plyalex/OpenFence/hardware/pcbs/MainCollar/MainCollarRender.jpg

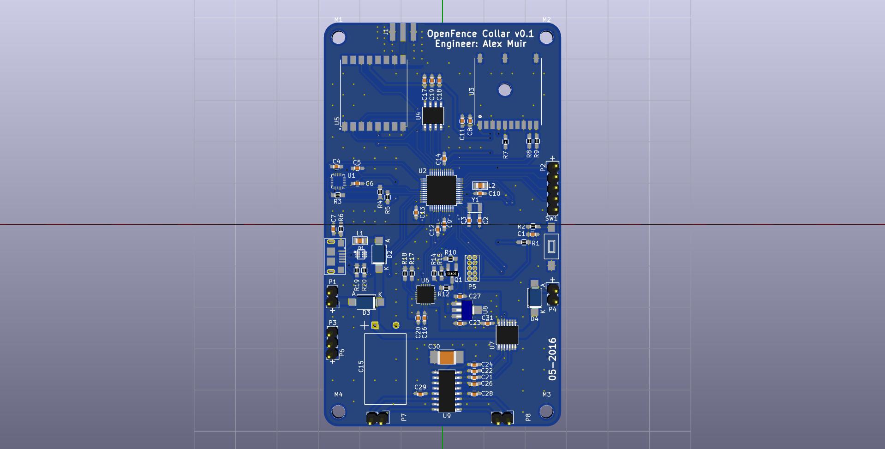
hardware/pcbs/MainCollar/MainCollarRender.jpg
