plyalex/OpenFence/hardware/solidworks/basestation/toplink.SLDPRT

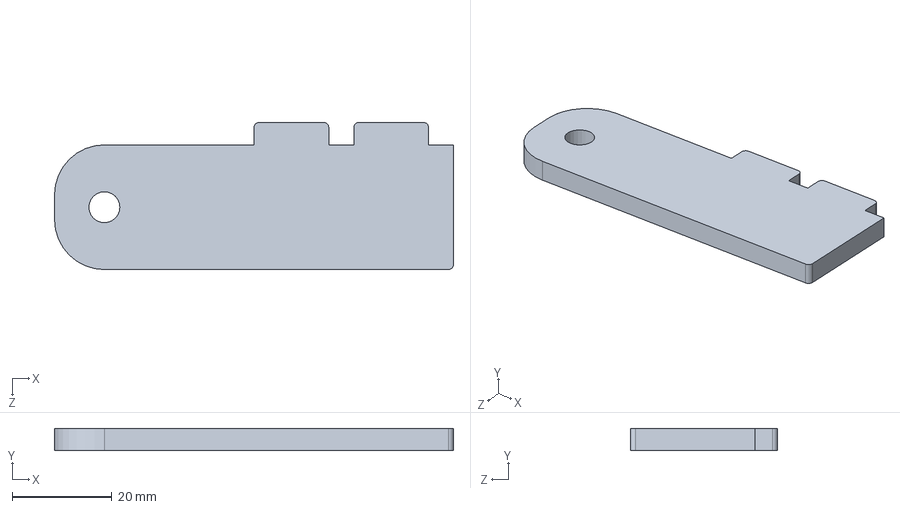
[picture p20: CAD file, 2016-09-19]
hardware/solidworks/basestation/toplink.SLDPRT
80.0 x 4.50 x 29.5 mm
