plyalex/OpenFence/hardware/solidworks/basestation/solarpanel.SLDPRT

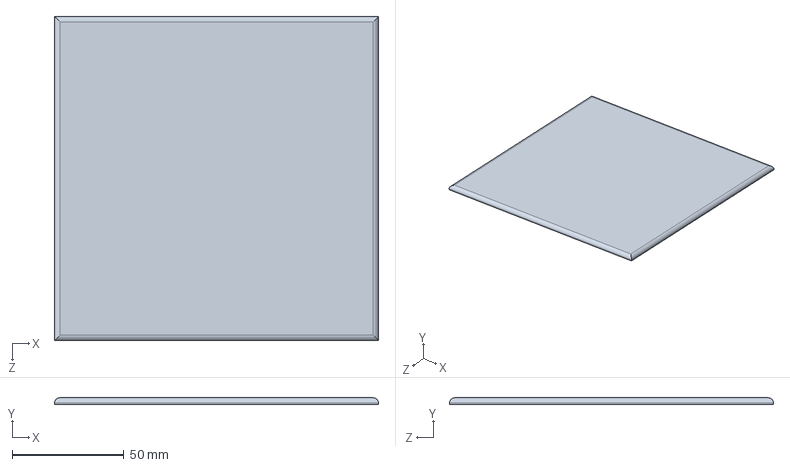
[picture p21: CAD file, 2016-09-19]
hardware/solidworks/basestation/solarpanel.SLDPRT
145.0 x 3.00 x 145.0 mm
